dilshan/arduino-superhet/design/radio-schematic/arduino-superhet/arduino-superhet.sch

## KiCad design design/radio-schematic/arduino-superhet/arduino-superhet.sch (2021-10-05)

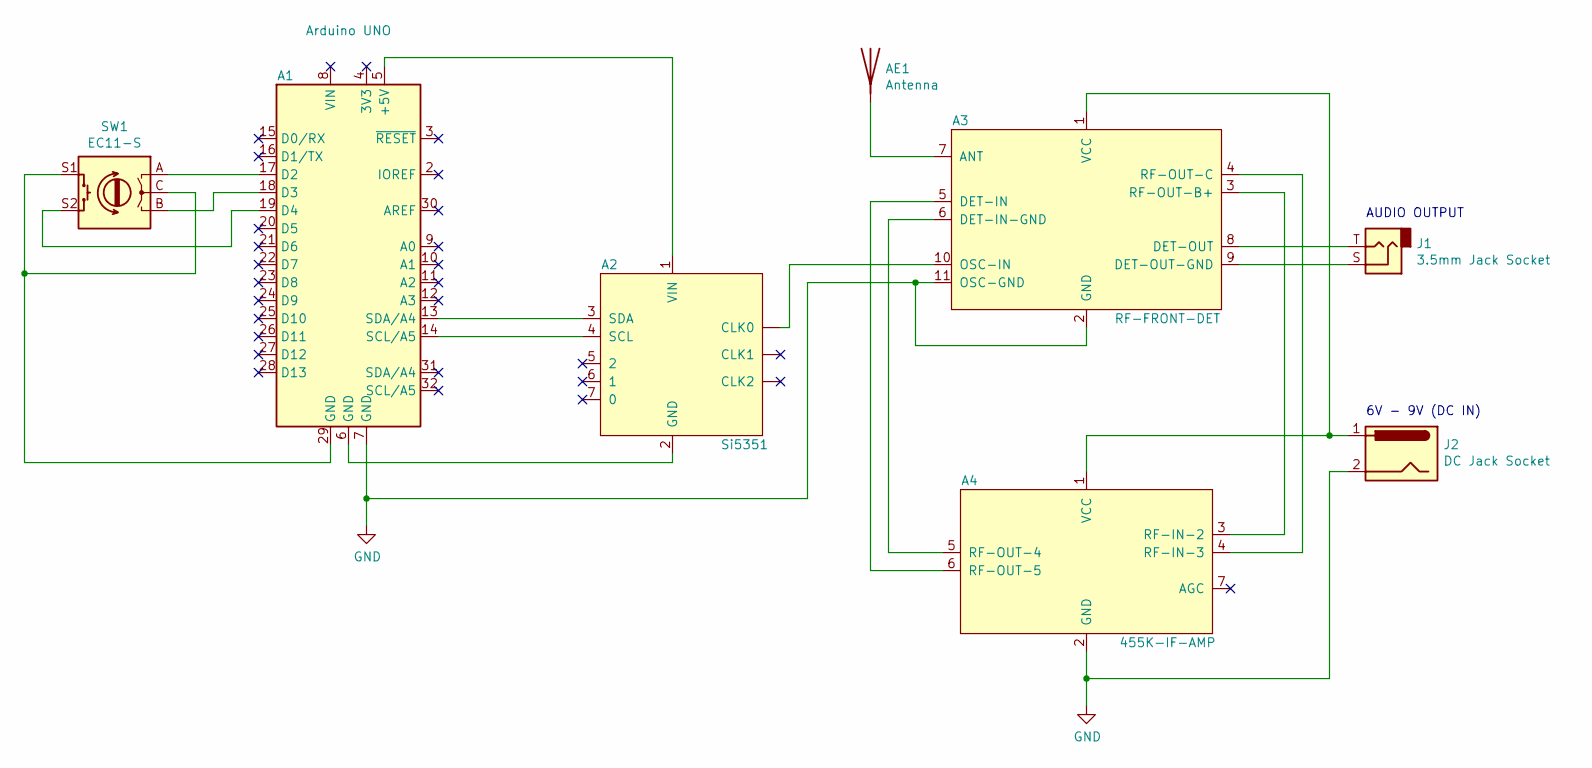
[picture p15: schematic arduino-superhet.sch]

Parts:
A1: Arduino UNO; Arduino_UNO_R3
A2: Si5351
A3: RF-FRONT-DET
A4: 455K-IF-AMP
AE1: Antenna
J1: 3.5mm Jack Socket
J2: DC Jack Socket
SW1: EC11-S

Connections:
GND: A1.7 (GND), A3.2 (GND), A3.11 (OSC-GND), A4.2 (GND), J2.2
unnamed: A1.5 (+5V), A2.1 (VIN)
unnamed: A1.6 (GND), A2.2 (GND)
unnamed: A1.13 (SDA/A4), A2.3 (SDA)
unnamed: A1.14 (SCL/A5), A2.4 (SCL)
unnamed: A1.17 (D2), SW1.A
unnamed: A1.18 (D3), SW1.B
unnamed: A1.19 (D4), SW1.S2
unnamed: A1.29 (GND), SW1.C, SW1.S1
unnamed: A2.~ (CLK0), A3.10 (OSC-IN)
unnamed: A3.1 (VCC), A4.1 (VCC), J2.1
unnamed: A3.3 (RF-OUT-B+), A4.3 (RF-IN-2)
unnamed: A3.4 (RF-OUT-C), A4.4 (RF-IN-3)
unnamed: A3.5 (DET-IN), A4.6 (RF-OUT-5)
unnamed: A3.6 (DET-IN-GND), A4.5 (RF-OUT-4)
unnamed: A3.7 (ANT), AE1.1
unnamed: A3.8 (DET-OUT), J1.T
unnamed: A3.9 (DET-OUT-GND), J1.S

Notes on the sheet:
AUDIO OUTPUT
6V - 9V (DC IN)
